kmontag/here2019/featherstream/src/WiFiHandler.cpp

#include "WiFiHandler.hpp"

#include <Arduino.h>
#include <FlashStorage.h>
#include <WiFi101.h>
#include <stdlib.h>

#include "secrets.h"

// Explicitly re-check connection status this often. Unclear whether
// checking all the time would actually be an issue - WiFi101 does
// something with a pending-event list on each check, though.
#define CONNECTION_VALID_MS 1000

using namespace featherstream;

FlashStorage(credentials_storage, WiFiHandler::credentials_t);

WiFiHandler::WiFiHandler(const FeatherstreamerManager &featherstreamerManager) : featherstreamerManager(featherstreamerManager) {
  this->credentials = credentials_storage.read();
  this->hasCredentials = (this->credentials.magic == EXPECTED_MAGIC);

  this->lastVerifiedAt = -CONNECTION_VALID_MS;
  this->isLastConnectionToMaster = false;
}

WiFiHandler::~WiFiHandler() {
}

bool WiFiHandler::isPaired() const {
  return this->hasCredentials;
}

bool WiFiHandler::ensureConnected() {
  if (this->isPaired()) {
    int32_t time = millis();

    if (time - this->lastVerifiedAt >= CONNECTION_VALID_MS) {
      uint8_t status = WiFi.status();
      if (status == WL_CONNECTED) {
        Serial.println("Verified WiFi connection.");
        this->lastVerifiedAt = time;
        return true;
      } else {
        Serial.println("Scanning networks...");
        int numSSIDs = WiFi.scanNetworks();
        if (numSSIDs == -1) {
          Serial.println("WiFi not available");
          return false;
        } else {
          bool foundPairedAP = false;
          bool foundMasterAP = false;

          for (int i = 0; i < numSSIDs; i++) {
            if (!foundPairedAP &&
                strcmp(this->getPairedSSID(), WiFi.SSID(i)) == 0) {
              foundPairedAP = true;
            }
            if (!foundMasterAP &&
                strcmp(this->getMasterSSID(), WiFi.SSID(i)) == 0) {
              foundMasterAP = true;
            }
          }

          if (foundPairedAP) {
            bool success = this->connect(this->getPairedSSID(), this->getPairedPassphrase());
            if (success) {
              this->isLastConnectionToMaster = false;
            }
            return success;
          } else if (foundMasterAP) {
            bool success = this->connect(this->getMasterSSID(), this->getMasterPassphrase());
            // When connecting to a master network, only succeed if
            // the network has the correct SSID.
            if (success) {
              const String ssid = this->featherstreamerManager.getReportedSSID(SECRET_MASTER_SERVER_IP, SECRET_SERVER_PORT);
              if (!ssid.equals(this->getPairedSSID())) {
                Serial.println("Connected to master network, but it did not report the correct SSID");
                success = false;
                WiFi.disconnect();
              }
            }
            if (success) {
              this->isLastConnectionToMaster = true;
            }
            return success;
          } else {
            Serial.print("Could not find ");
            Serial.print(this->getPairedSSID());
            Serial.print(" or ");
            Serial.println(this->getMasterSSID());
            return false;
          }
        }
      }
    } else {
      // Recently verified.
      return true;
    }
  } else {
    Serial.println("Cannot connect to WiFi, we're not paired with a device.");
    return false;
  }
}

bool WiFiHandler::connect(const char *ssid, const char *passphrase) {
  uint32_t timeout = 10000;
  uint32_t startTime = millis();

  uint8_t status = WL_IDLE_STATUS;
  while (status != WL_CONNECTED) {
    if (millis() - startTime > timeout) {
      Serial.println("Connection timed out.");
      return false;
    }

    Serial.print("Current status is: ");
    Serial.print(status);
    Serial.print(". Attempting to connect to SSID: ");
    Serial.println(ssid);

    status = WiFi.begin(ssid, passphrase);

    if (status != WL_CONNECTED) {
      delay(2000);
    }
  }

  Serial.println("Successfully connected to WiFi");

  // print the SSID of the network you're attached to:
  Serial.print("SSID: ");
  Serial.println(WiFi.SSID());

  // print your WiFi shield's IP address:
  IPAddress ip = WiFi.localIP();
  Serial.print("IP Address: ");
  Serial.println(ip);

  // print the received signal strength:
  long rssi = WiFi.RSSI();
  Serial.print("signal strength (RSSI):");
  Serial.print(rssi);
  Serial.println(" dBm");

  return true;
}

bool WiFiHandler::setPairedSSID(const char *ssid) {
  if (strlen(ssid) > SSID_MAX_LENGTH) {
    Serial.println("SSID is too long to store");
    return false;
  // } else if (strlen(passphrase) > PASSPHRASE_MAX_LENGTH) {
  //   Serial.println("Passphrase is too long to store");
  //   return false;
  } else {
    memset(this->credentials.ssid, 0, sizeof(this->credentials.ssid));
    memset(this->credentials.passphrase, 0, sizeof(this->credentials.passphrase));

    strcpy(this->credentials.ssid, ssid);
    //strcpy(this->credentials.passphrase, passphrase);
    strcpy(this->credentials.passphrase, SECRET_PAIRED_PASSPHRASE);
    this->credentials.magic = EXPECTED_MAGIC;

    credentials_storage.write(this->credentials);
    this->hasCredentials = true;

    Serial.println("Updated paired credentials");
    return true;
  }
}

const char * WiFiHandler::getPairedSSID() const {
  if (this->hasCredentials) {
    return this->credentials.ssid;
  } else {
    return NULL;
  }
}

inline const char * WiFiHandler::getMasterSSID() const {
  return SECRET_MASTER_SSID;
}

inline const char * WiFiHandler::getPairedPassphrase() const {
  if (this->hasCredentials) {
    return this->credentials.passphrase;
  } else {
    return NULL;
  }
}

inline const char * WiFiHandler::getMasterPassphrase() const {
  return SECRET_MASTER_PASSPHRASE;
}

IPAddress WiFiHandler::getServerAddress() const {
  if (this->isLastConnectionToMaster) {
    return SECRET_MASTER_SERVER_IP;
  } else {
    return SECRET_PAIRED_SERVER_IP;
  }
}
