kmontag/here2019/featherstream/include/secrets.h

#pragma once

#define SECRET_SERVER_PORT 44668

#define SECRET_PAIRED_PASSPHRASE "feath3rstr"
#define SECRET_PAIRED_SERVER_IP IPAddress(192, 168, 8, 1)

#define SECRET_PAIRING_SSID "_featherstreamer-pairing"
#define SECRET_PAIRING_PASSPHRASE "feath3rstr"
#define SECRET_PAIRING_SERVER_IP IPAddress(192, 168, 8, 1)

#define SECRET_MASTER_SSID "_featherstreamer-master"
#define SECRET_MASTER_PASSPHRASE "feath3rstr"
#define SECRET_MASTER_SERVER_IP IPAddress(192, 168, 9, 1)

#include "secrets.local.h"
